rahimkhoja/MANPADS-System-Launcher-and-Rocket/cad/launcher_tube.stl

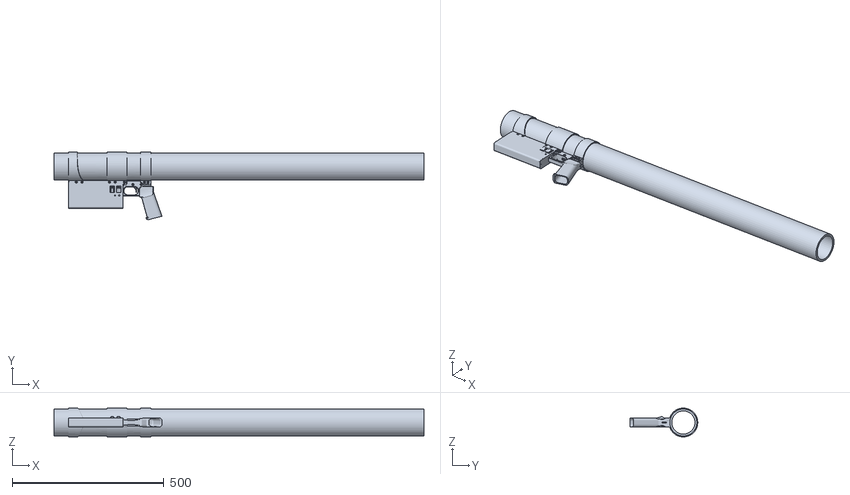
[picture p16: CAD file, 2026-03-29]
cad/launcher_tube.stl
1219.2 x 222.6 x 95.1
