rahimkhoja/MANPADS-System-Launcher-and-Rocket/cad/imu_mpu6050.stl

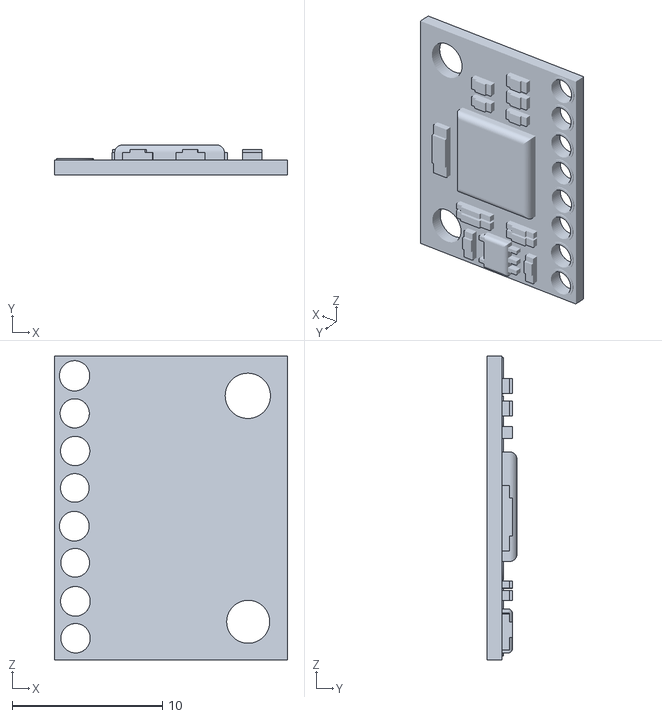
[picture p17: CAD file, 2026-03-29]
cad/imu_mpu6050.stl
15.6 x 2.00 x 20.3
