rahimkhoja/MANPADS-System-Launcher-and-Rocket/cad/nozzle_body.stl

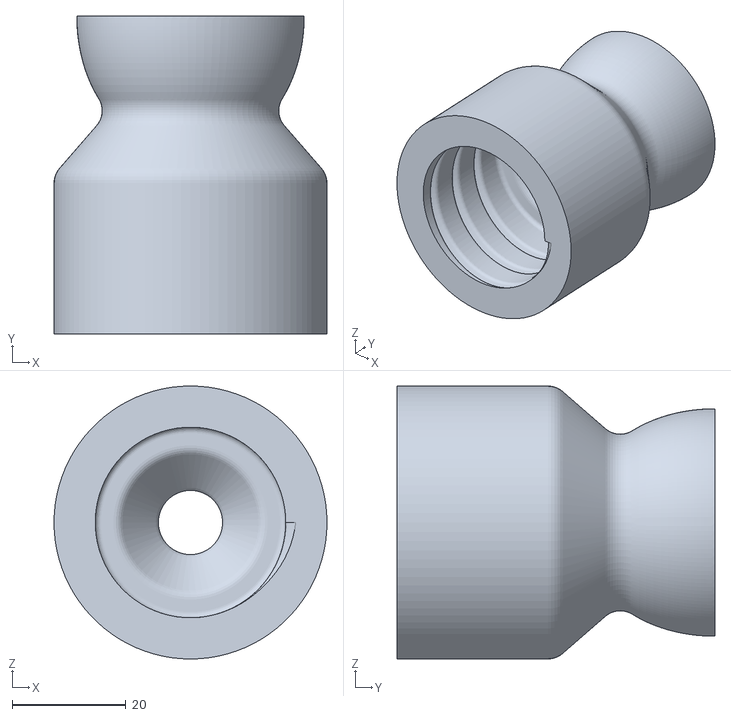
[picture p18: CAD file, 2026-03-29]
cad/nozzle_body.stl
48.0 x 55.9 x 48.0
