rahimkhoja/MANPADS-System-Launcher-and-Rocket/cad/servo_sg90_arm_2.stl

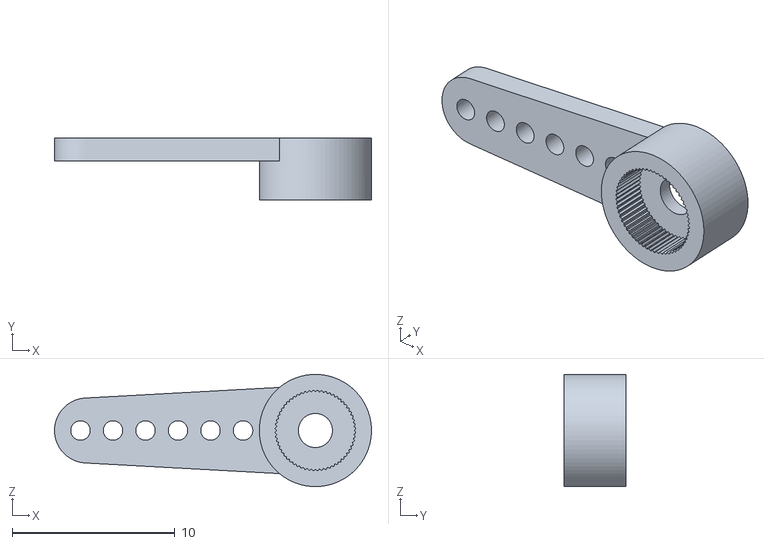
[picture p19: CAD file, 2026-03-29]
cad/servo_sg90_arm_2.stl
19.5 x 3.80 x 6.90
