rahimkhoja/MANPADS-System-Launcher-and-Rocket/cad/tactile_switch.stl

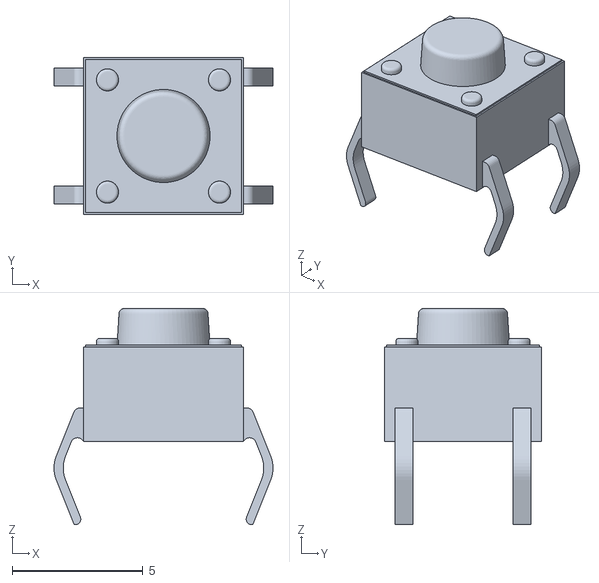
[picture p20: CAD file, 2026-03-29]
cad/tactile_switch.stl
8.37 x 5.99 x 8.26
